mmagyar/music-gadget-encoder/Src/seq/seq.c

#include "seq.h"
#include "../util/safe_array.h"
#include "../util/midi/midi.h"
#include "../util/midi/midi_enums.h"
#include "stdint.h"
#include "arm_math.h"
#include "../system/inputs.h"
#include "../system/led_update.h"

Seq seq = {
COUNTER_WRAP_AROUND(7),
COUNTER_SATURATE(31),
COUNTER_SATURATE( SEQ_LEVELS - 1),
true, 120, 0, 0, { { { 0 } } } };

//{{{255,-128},{255,INT8_MAX},{255,128},{255,127}}}
Midi_note notes[SEQ_LEVELS] = {
        C2,  //Bass drum
        D2,  //Snare
        Fs2, //Closed hi hat
        As2, //Open hi hat
        };

Midi_channel channel = CH10;
Midi_cc_number cc = CC_CH_046;
#define max_parts 8

void seq_next_part();
void seq_prev_part();
void seq_next_level();
void seq_prev_level();

void animate_flash(u8 data, Seq_animation * animation, bool light_variant);
Seq_animation anim;


u16 bpm_to_4th_ms(u8 bpm) {
    return 60000 / bpm;
}

inline void seq_next_part() {
    counter_inc(&seq.cursor);
}

inline void seq_prev_part() {
    counter_dec(&seq.cursor);
}

inline void seq_next_level() {
    counter_inc(&seq.current_level);
}

inline void seq_prev_level() {
    counter_dec(&seq.current_level);
}

void animate_top_bar() {
    if (anim.need_run) {
        u32 current_time = (u32) seq.current_ms & 0xFFFFFFFF;
        if (!anim.start_time) {
            anim.start_time = current_time;
        }
        u32 run_time = current_time - anim.start_time;
        u16 speed = anim.speed * 10;
        u16 current_frame = run_time / speed;
        bool show = true;

        switch (anim.anim) {
        case SEQ_ANIM_SHOW_NUM:
            loop(x,32)
            {
                display.top_bar_precise[x] = x >> 2 == anim.data ? IN_HIGH : IN_OFF;
            }
            break;
        case SEQ_ANIM_FLASH_NUM:
            if (current_frame % 2) show = false;
            loop(x, 32)
            {
                display.top_bar_precise[x] =
                        x >> 2 == anim.data && show && (anim.light_pattern & (1 << (x % 4))) ?
                                IN_HIGH : IN_OFF;
            }
            break;
        default: //Should not happen
            break;
        }


        if (anim.start_time + (anim.length * 10) <= current_time) {
            anim.start_time = 0;
            anim.need_run = false;
        }

    }
}
void stop_playback() {
    seq.playing = false;
    loop(x, SEQ_LEVELS)
    {
        send_note_off(CH10, notes[x], 127);
    }

}

void start_playback() {
    seq.playing = true;
    //TODO start needs to continue where it left off
    u16 sixteenth = bpm_to_4th_ms(seq.bpm) / 4;
    seq.start_ms = seq.current_ms - (sixteenth * seq.position.data);
}

/**
 * Returns true if position is update, false if it's the same
 */
bool update_seq_position() {
    u32 cms = seq.current_ms;

    if (cms < seq.start_ms) {
        //printf("Invalid sequencer status, current: %d behind start ms: %d, "
          //      "resetting start to current of %d\r\n", cms, seq.start_ms, seq.current_ms);
        seq.start_ms = cms;
    }
    u16 sixteenth = bpm_to_4th_ms(seq.bpm) / 4;
    u32 playback_ms = cms - seq.start_ms;
    u16 current_pos = playback_ms / sixteenth;
    bool result = current_pos != seq.position.data;
    if (current_pos >= 32) {

        seq.start_ms += sixteenth * 32;
        update_seq_position();
    } else {
        counter_set(current_pos, &seq.position);
    }
    return result;
}
void update_seq() {

    if (seq.playing) {
        if (update_seq_position()) send_midi();
    }

    if (button_pressed[0]) {
        button_pressed[0]--;
        stop_playback();
    }

    if (button_pressed[1]) {
        button_pressed[1]--;
        start_playback();
    }

    if (button_pressed[5]) {
        button_pressed[5]--;
        seq_next_part();
        animate_flash(seq.cursor.data, &anim, false);
    }

    if (button_pressed[2]) {
        button_pressed[2]--;
        seq_prev_part();
        animate_flash(seq.cursor.data, &anim, false);
    }

    if (button_pressed[3]) {
        button_pressed[3]--;
        seq_prev_level();
        animate_flash(seq.current_level.data, &anim, true);
    }

    if (button_pressed[4]) {
        button_pressed[4]--;
        seq_next_level();
        animate_flash(seq.current_level.data, &anim, true);
    }

    loop(x,4)
    {
        s16 * step = &encoders[x].encoder_step;

        if (!encoders[x].s) {
            s16 increment = 64;
            u8 * velo = &seq.points[seq.current_level.data][x + (seq.cursor.data * 4)].velocity;
            while (*step) {
                if (*step > 0) {
                    if (((u32) (*velo)) + increment > 0xFF) *velo = UINT8_MAX;
                    else *velo += increment;
                    *step -= 1;
                } else {
                    if (((s32) (*velo)) - increment < 0) *velo = 0x00;
                    else *velo -= increment;
                    *step += 1;
                }
            }
        } else {
            s8 * pitch = &seq.points[seq.current_level.data][x + (seq.cursor.data * 4)].pitch;
            s16 increment = 16;
            while (*step) {
                if (*step > 0) {
                    if (((s32) (*pitch)) + increment > INT8_MAX) *pitch = INT8_MAX;
                    else *pitch += increment;
                    *step -= 1;
                } else {
                    if (((s32) (*pitch)) - increment < INT8_MIN) *pitch = INT8_MIN;
                    else *pitch -= increment;
                    *step += 1;
                }
            }
            //Close enough to zero to be considered 0;
            if (*pitch < 0 + (increment / 2) && *pitch > 0 - (increment / 2)) {
                *pitch = 0;
            }
        }
    }

    loop(x, 32)
    {
        Intensity intensity = IN_OFF;
        u8 vel = seq.points[seq.current_level.data][x].velocity;
        if (vel) {
            if (vel < 64) {
                intensity = IN_LOW;
            } else if (vel < 128) {
                intensity = IN_LOW_MED;
            } else if (vel < 192) {
                intensity = IN_HIGH_MED;
            } else {
                intensity = IN_HIGH;
            }
        }

        display.top_bar_precise[x] = intensity;

        if (seq.playing) {
            if (seq.position.data == x) {
                if (display.top_bar_precise[x] != IN_LOW) {
                    display.top_bar_precise[x] = IN_LOW;
                } else {
                    display.top_bar_precise[x] = IN_HIGH_MED;
                }
            }
        }
    }

    loop(x,4)
    {
        Seq_event * seq_event = &seq.points[seq.current_level.data][x + (seq.cursor.data * 4)];
        led_calculate_bar_16(seq_event->velocity, display.encoders[x].red_precise);
        led_calculate_bar_signed_16(seq_event->pitch, display.encoders[x].green_precise);
        loop(y,16)
        {

        }
    }

    animate_top_bar();
}

void animate_flash(u8 data, Seq_animation * animation, bool light_variant) {
    animation->need_run = true;
    animation->data = data;
    animation->speed = 7;
    animation->length = 50;
    animation->start_time = 0;
    animation->light_pattern = light_variant ? 0xF : 0x9;
    animation->anim = SEQ_ANIM_FLASH_NUM;

}

void send_midi() {

    loop(x,seq.current_level.data_max +1)
    {

        Seq_event * ev = &seq.points[x][seq.position.data];
        //Send note off if previous was on
        if (seq.position.data == 0) {
            if (seq.points[x][seq.position.data_max].velocity) {
                send_note_off(channel, notes[x], 127);
            }
        } else {
            if (seq.points[x][seq.position.data - 1].velocity) {
                send_note_off(channel, notes[x], 127);
            }
        }
        //Send not on if velocity is non zero
        if (ev->velocity) {
            u8 u_pitch = (ev->pitch + ((u16) (INT8_MAX - 1))) > 1;

            if (ev->pitch) send_cc(channel, ((u8) cc) + x, u_pitch);

            send_note_on(channel, notes[x], ev->velocity >> 1);
        }

    }

}
